merlin-rce/Dyce/Web simulation/assets/gallery/pcb-irl-bottom.jpg

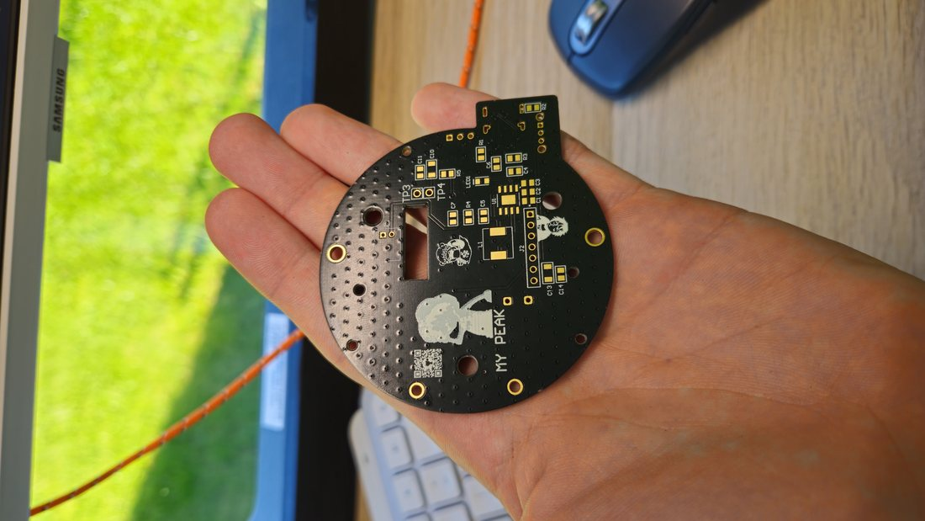
Web simulation/assets/gallery/pcb-irl-bottom.jpg
