merlin-rce/Dyce/Web simulation/assets/gallery/pcb-irl-global.jpg

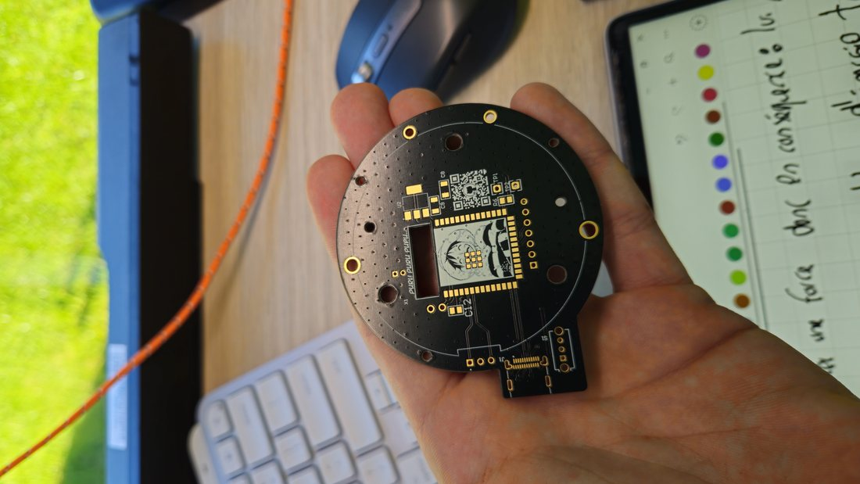
Web simulation/assets/gallery/pcb-irl-global.jpg
