merlin-rce/Dyce/Web simulation/assets/gallery/pcb-irl-top.jpg

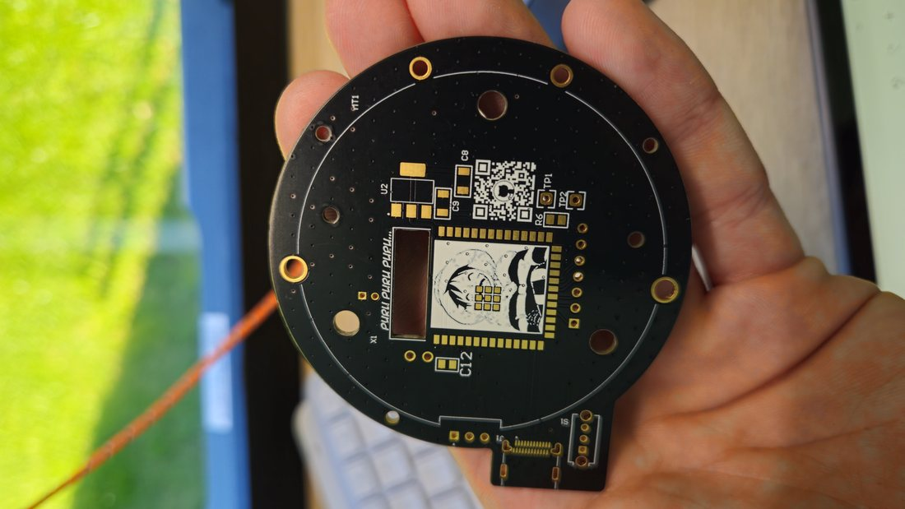
Web simulation/assets/gallery/pcb-irl-top.jpg
