merlin-rce/Dyce/Web simulation/assets/qr.png

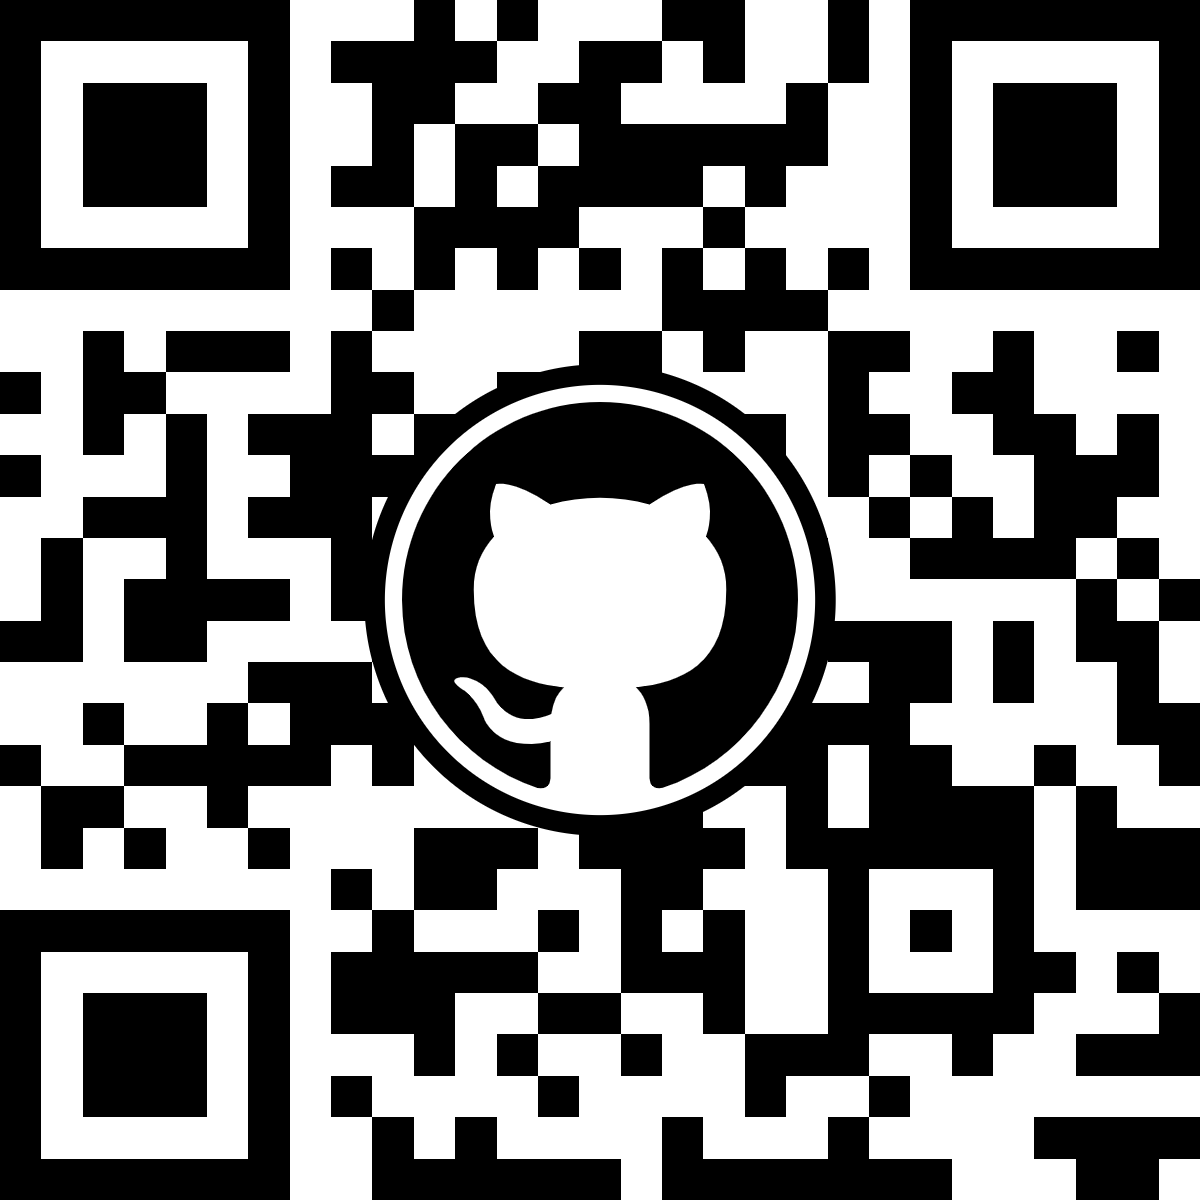
Web simulation/assets/qr.png
