merlin-rce/Dyce/Firmware/src/icon.h

#pragma once
// ICON - genere depuis Frame 2.svg (logo DYCE), fond marine integre
#define ICON_W 84
#define ICON_H 85
static const unsigned short ICON[] = {
0x1149,0x1149,0x1149,0x1149,0x1149,0x1149,0x1149,0x1149,0x1149,0x1149,0x1149,0x1149,0x1149,0x1149,0x1149,0x1149,
0x1149,0x1149,0x1149,0x1149,0x1149,0x1149,0x1149,0x1149,0x1149,0x1149,0x1149,0x1149,0x1148,0x1128,0x1149,0x1149,
0x1149,0x1149,0x1128,0x0928,0x0907,0x0907,0x08e6,0x08e6,0x1106,0x1106,0x1106,0x10e6,0x08e6,0x08e6,0x0907,0x0907,
0x0928,0x0928,0x1149,0x1149,0x1149,0x1149,0x1128,0x1148,0x1149,0x1149,0x1149,0x1149,0x1149,0x1149,0x1149,0x1149,
0x1149,0x1149,0x1149,0x1149,0x1149,0x1149,0x1149,0x1149,0x1149,0x1149,0x1149,0x1149,0x1149,0x1149,0x1149,0x1149,
0x1149,0x1149,0x1149,0x1149,0x1149,0x1149,0x1149,0x1149,0x1149,0x1149,0x1149,0x1149,0x1149,0x1149,0x1149,0x1149,
0x1149,0x1149,0x1149,0x1149,0x1149,0x1149,0x1149,0x1149,0x1149,0x1149,0x1149,0x1149,0x1149,0x1149,0x1149,0x1149,
0x1149,0x1149,0x1149,0x0907,0x08c5,0x10e5,0x3a2a,0x52ac,0x634e,0x6b8f,0x6b6e,0x8452,0x9cf4,0x9cf5,0x9d15,0x9cf4,
0x8c93,0x6b8e,0x6b8f,0x634e,0x52cc,0x3a4a,0x1106,0x08c5,0x0907,0x1149,0x1149,0x1149,0x1149,0x1149,0x1149,0x1149,
0x1149,0x1149,0x1149,0x1149,0x1149,0x1149,0x1149,0x1149,0x1149,0x1149,0x1149,0x1149,0x1149,0x1149,0x1149,0x1149,
0x1149,0x1149,0x1149,0x1149,0x1149,0x1149,0x1149,0x1149,0x1149,0x1149,0x1149,0x1149,0x1149,0x1149,0x1149,0x1149,
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
0x9cf4,0xe75f,0xef9f,0xe73e,0xdf3e,0xe75e,0xe75e,0xe75e,0xe75e,0xe75e,0xe75e,0xe75e,0xe75e,0xe75e,0xe75e,0xe75e,
0xe75e,0xe75e,0xe75e,0xe75e,0xe75e,0xe75e,0xe75e,0xe75e,0xe75e,0xe75e,0xe75e,0xe75e,0xe75e,0xe75e,0xe75e,0xe75e,
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
};
