merlin-rce/Dyce/Firmware/src/logo.h

#pragma once
// LOGO - genere depuis Frame 2.svg (logo DYCE), fond marine integre
#define LOGO_W 200
#define LOGO_H 104
static const unsigned short LOGO[] = {
0x1149,0x1149,0x1149,0x1149,0x1149,0x1149,0x1149,0x1149,0x1149,0x1149,0x1149,0x1149,0x1149,0x1149,0x1149,0x1149,
0x1149,0x1149,0x1149,0x1149,0x1149,0x1149,0x1149,0x1149,0x1149,0x1149,0x1149,0x1149,0x1149,0x1149,0x1149,0x1149,
0x1149,0x1149,0x1148,0x1128,0x1149,0x1149,0x1149,0x1149,0x1149,0x0907,0x08e6,0x08c5,0x08a4,0x0083,0x0062,0x1905,
0x2146,0x4229,0x39e7,0x39c7,0x39c7,0x39e7,0x4209,0x2966,0x1905,0x0062,0x0063,0x08a4,0x08c5,0x08e6,0x0907,0x1149,
0x1149,0x1149,0x1149,0x1149,0x1128,0x1148,0x1149,0x1149,0x1149,0x1149,0x1149,0x1149,0x1149,0x1149,0x1149,0x1149,
0x1149,0x1149,0x1149,0x1149,0x1149,0x1149,0x1149,0x1149,0x1149,0x1149,0x1149,0x1149,0x1149,0x1149,0x1149,0x1149,
0x1149,0x1149,0x1149,0x1149,0x1149,0x1149,0x1149,0x1149,0x1149,0x1149,0x1149,0x1149,0x1149,0x1149,0x1149,0x1149,
0x1149,0x1149,0x1149,0x1149,0x1149,0x1149,0x1149,0x1149,0x1149,0x1149,0x1149,0x1149,0x1149,0x1149,0x1149,0x1149,
0x1149,0x1149,0x1149,0x1149,0x1149,0x1149,0x1149,0x1149,0x1149,0x1149,0x1149,0x1149,0x1149,0x1149,0x1149,0x1149,
0x1149,0x1149,0x1149,0x1149,0x1149,0x1149,0x1149,0x1149,0x1149,0x1149,0x1149,0x1149,0x1149,0x1149,0x1149,0x1149,
0x1149,0x1149,0x1149,0x1149,0x1149,0x1149,0x1149,0x1149,0x1149,0x1149,0x1149,0x1149,0x1149,0x1149,0x1149,0x1149,
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
0x1149,0x1149,0x1149,0x1149,0x1149,0x1149,0x1149,0x1149,0x1149,0x1149,0x1149,0x1149,0x1149,0x1149,0x1149,0x1149,
0x1149,0x1149,0x1149,0x1148,0x1148,0x1149,0x1149,0x0928,0x08c5,0x0062,0x2125,0x6b8e,0xb5d8,0xdf1d,0xf7df,0xf7bf,
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

};
