merlin-rce/Dyce/Firmware/src/qr_image.h

#pragma once
// Image QR reelle (github.com/merlin-rce) - generee depuis QR-for-merlin-rce.png
// bit=1 -> pixel noir. Largeur paddee a l'octet.
#define QR_IMG_W 166
#define QR_IMG_H 166
static const unsigned char QR_IMG[] = {
0xff,0xff,0xff,0xff,0xff,0x00,0x00,0x7e,0x07,0xc0,0x00,0x0f,0xfe,0x00,0x1f,0x03,0xff,0xff,0xff,0xff,
0xfc,0xff,0xff,0xff,0xff,0xff,0x00,0x00,0x7e,0x07,0xc0,0x00,0x0f,0xfe,0x00,0x1f,0x03,0xff,0xff,0xff,
0xff,0xfc,0xff,0xff,0xff,0xff,0xff,0x00,0x00,0x7e,0x07,0xc0,0x00,0x0f,0xfe,0x00,0x1f,0x03,0xff,0xff,
0xff,0xff,0xfc,0xff,0xff,0xff,0xff,0xff,0x00,0x00,0x7e,0x07,0xc0,0x00,0x0f,0xfe,0x00,0x1f,0x03,0xff,
0xff,0xff,0xff,0xfc,0xff,0xff,0xff,0xff,0xff,0x00,0x00,0x7e,0x07,0xc0,0x00,0x0f,0xfe,0x00,0x1f,0x03,
0xff,0xff,0xff,0xff,0xfc,0xff,0xff,0xff,0xff,0xff,0x00,0x00,0x7e,0x07,0xc0,0x00,0x0f,0xfe,0x00,0x1f,
0x03,0xff,0xff,0xff,0xff,0xfc,0xfc,0x00,0x00,0x00,0x3f,0x03,0xff,0xff,0xf8,0x00,0xff,0xf0,0x7e,0x00,
0x1f,0x03,0xf0,0x00,0x00,0x00,0xfc,0xfc,0x00,0x00,0x00,0x3f,0x03,0xff,0xff,0xf8,0x00,0xff,0xf0,0x7e,
0x00,0x1f,0x03,0xf0,0x00,0x00,0x00,0xfc,0xfc,0x00,0x00,0x00,0x3f,0x03,0xff,0xff,0xf8,0x00,0xff,0xf0,
0x7e,0x00,0x1f,0x03,0xf0,0x00,0x00,0x00,0xfc,0xfc,0x00,0x00,0x00,0x3f,0x03,0xff,0xff,0xf8,0x00,0xff,
0xf0,0x7e,0x00,0x1f,0x03,0xf0,0x00,0x00,0x00,0xfc,0xfc,0x00,0x00,0x00,0x3f,0x03,0xff,0xff,0xf8,0x00,
0xff,0xf0,0x7e,0x00,0x1f,0x03,0xf0,0x00,0x00,0x00,0xfc,0xfc,0x0f,0xff,0xf0,0x3f,0x00,0x1f,0xfe,0x00,
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
0xff,0x03,0xe0,0x7e,0x07,0xc0,0xfc,0x0f,0x81,0xf8,0x1f,0x03,0xff,0xff,0xff,0xff,0xfc,0xff,0xff,0xff,
0xff,0xff,0x03,0xe0,0x7e,0x07,0xc0,0xfc,0x0f,0x81,0xf8,0x1f,0x03,0xff,0xff,0xff,0xff,0xfc,0xff,0xff,
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
};
